AmigusLabs/medidorCO2/3D/view1.png

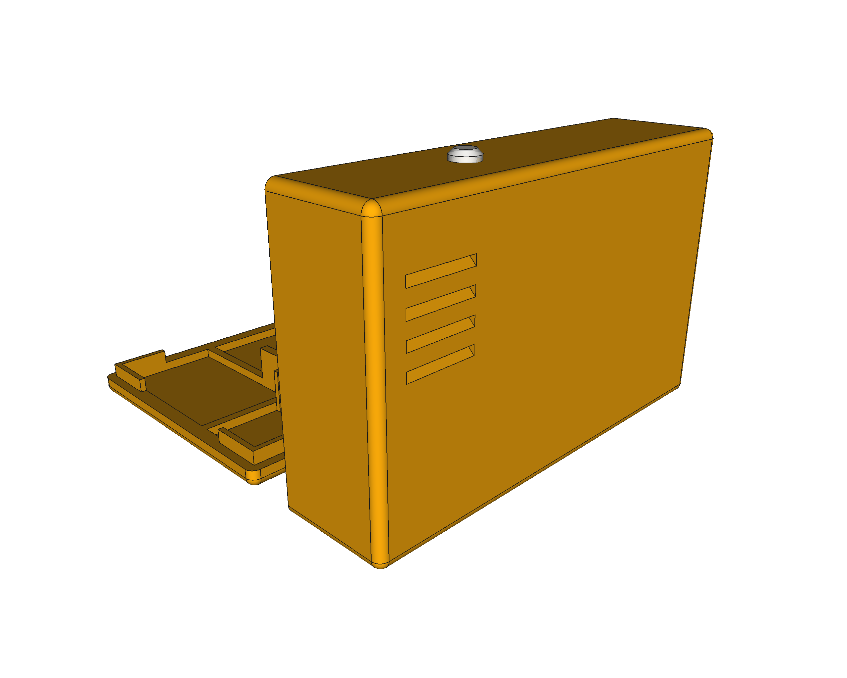
3D/view1.png
