AmigusLabs/medidorCO2/3D/view2.png

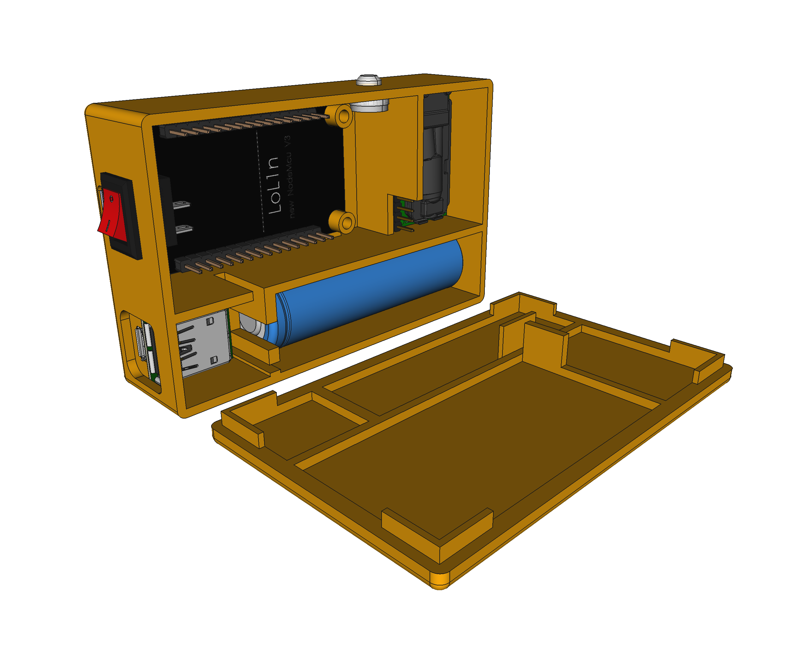
3D/view2.png
