AmigusLabs/medidorCO2/3D/view3.png

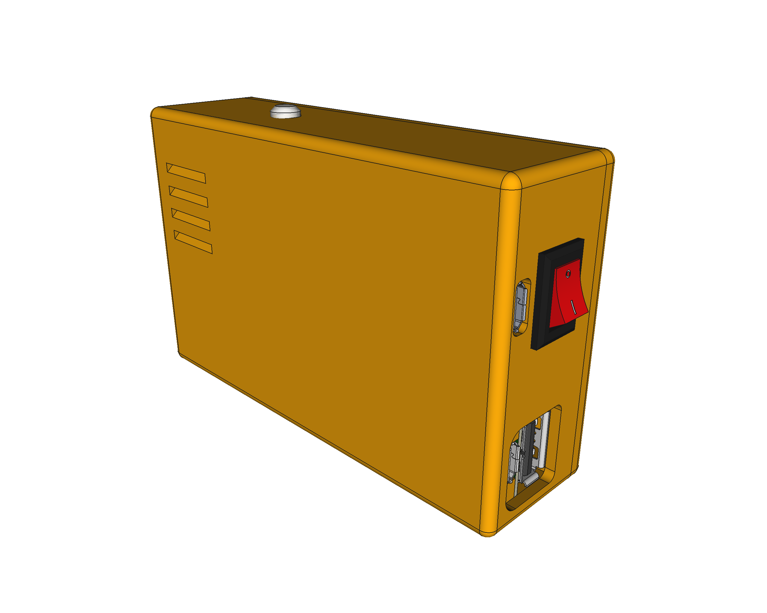
3D/view3.png
