AmigusLabs/medidorCO2/montaje/montaje_medidor_CO2.png

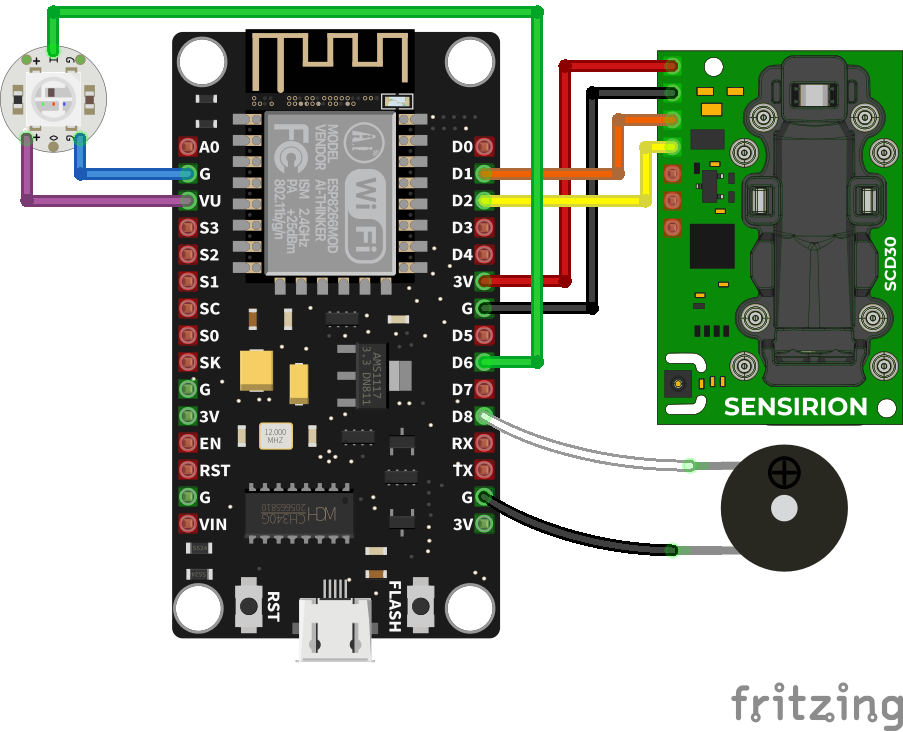
montaje/montaje_medidor_CO2.png
